LaubachLab/OpenSourceSyringePump/3D Printed Parts for Syringe Holder/60cc syringe body holder.stl

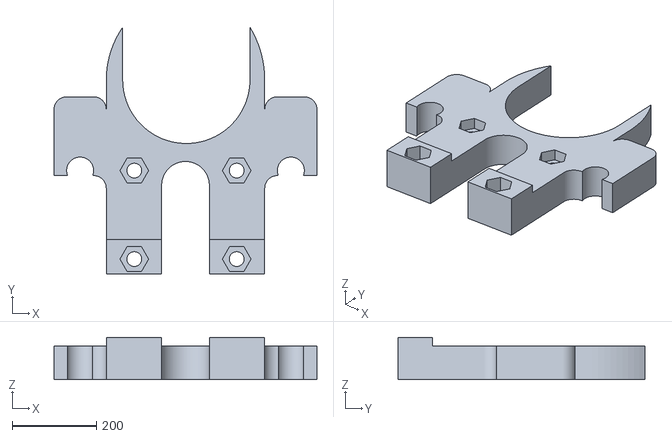
[picture p13: CAD file, 2019-06-21]
3D Printed Parts for Syringe Holder/60cc syringe body holder.stl
624.0 x 585.2 x 100.0
