LaubachLab/OpenSourceSyringePump/3D Printed Parts for Syringe Holder/blade.stl

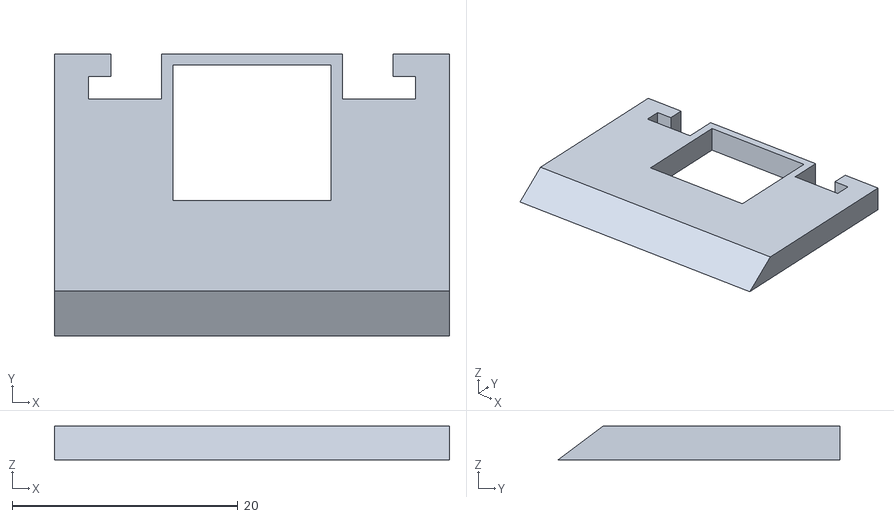
[picture p14: CAD file, 2019-06-21]
3D Printed Parts for Syringe Holder/blade.stl
35.0 x 25.0 x 3.00
